gutbag/BMW_TomTom_Adaptor/BMW_TomTom_Adaptor-TomTomLocatorBlockBuckConverterRecess001.step

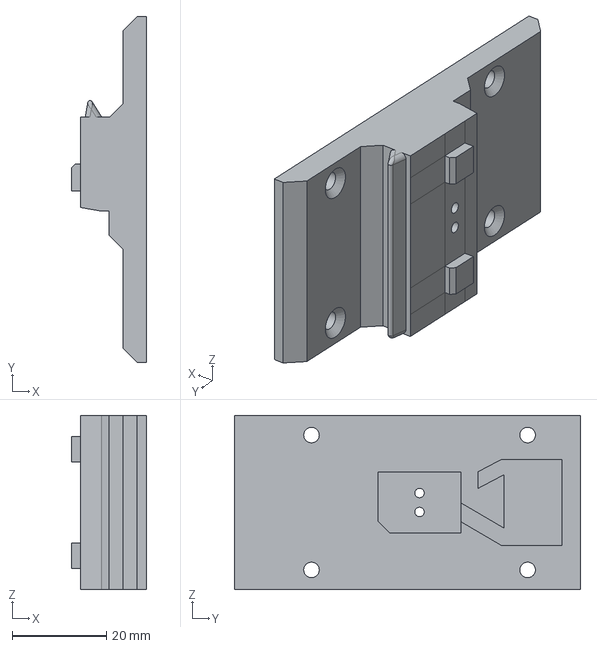
[picture p16: CAD file, 2025-10-08]
BMW_TomTom_Adaptor-TomTomLocatorBlockBuckConverterRecess001.step
15.9 x 73.4 x 37.0 mm
